nicolailund/PalletProof/src/pallet_video_recorder/config.py

from __future__ import annotations

import tomllib
from dataclasses import dataclass, field
from pathlib import Path
import re
from typing import Any


@dataclass(frozen=True)
class CameraConfig:
    backend: str = "auto"
    width: int = 1920
    height: int = 1080
    preview_width: int = 1280
    preview_height: int = 720
    fps: int = 30
    bitrate: int = 12_000_000
    opencv_device: int = 0
    opencv_fourcc: str = "MJPG"
    autofocus_mode: str = "continuous"
    autofocus_range: str = "full"
    autofocus_speed: str = "fast"


@dataclass(frozen=True)
class BarcodeConfig:
    enabled: bool = False
    scan_every_n_frames: int = 2
    min_chars: int = 4
    max_chars: int = 64
    accepted_pattern: str = r"^[A-Za-z0-9_.()$/+%-]+$"
    roi: tuple[float, float, float, float] = (0.0, 0.0, 1.0, 1.0)
    rotation_degrees: tuple[int, ...] = (
        0,
        90,
        180,
        270,
        15,
        345,
        30,
        330,
    )
    formats: tuple[str, ...] = (
        "Code128",
        "Code39",
        "Code93",
        "Codabar",
        "ITF",
        "EAN13",
        "EAN8",
        "UPCA",
        "UPCE",
        "QRCode",
        "DataMatrix",
        "PDF417",
    )
    scan_scales: tuple[float, ...] = (1.0,)
    preprocess: bool = False
    confirm_read_count: int = 2
    confirm_window_seconds: float = 1.5
    duplicate_suppress_seconds: float = 8.0
    ambient_suppress_seconds: float = 2.0
    ambient_absent_seconds: float = 2.0
    validate_gs1_ai01_check_digit: bool = True


@dataclass(frozen=True)
class HardwareScannerConfig:
    enabled: bool = True
    mode: str = "auto"
    device: str = "auto"
    baudrate: int = 115200
    reconnect_seconds: float = 5.0
    line_idle_seconds: float = 0.25
    trigger_gpio_enabled: bool = False
    trigger_gpio_pin: int = 23
    trigger_interval_seconds: float = 2.0
    trigger_pulse_seconds: float = 0.15
    trigger_active_high: bool = False
    duplicate_suppress_seconds: float = 2.0
    min_chars: int = 4
    max_chars: int = 512
    accepted_pattern: str = r"^[A-Za-z0-9_.()$/+%-]+$"
    validate_gs1_ai01_check_digit: bool = True


@dataclass(frozen=True)
class MotionConfig:
    roi: tuple[float, float, float, float] = (0.08, 0.08, 0.84, 0.84)
    threshold: float = 0.018
    still_seconds: float = 4.0
    minimum_recording_seconds: float = 30.0
    maximum_recording_seconds: float = 180.0
    require_motion_before_stop: bool = True


@dataclass(frozen=True)
class RecordingConfig:
    root_dir: Path = Path("data")
    file_extension: str = ".mp4"


@dataclass(frozen=True)
class DeviceConfig:
    provisioning_required: bool = False
    identity_file: Path = Path("device_identity.json")
    serial_number: str = "UNPROVISIONED"
    provisioning_qr_prefix: str = "PALLETPROOF"


@dataclass(frozen=True)
class CloudConfig:
    enabled: bool = False
    supabase_url: str = ""
    supabase_anon_key: str = ""
    heartbeat_interval_seconds: float = 60.0
    request_timeout_seconds: float = 10.0
    temperature_file: Path = Path("/sys/class/thermal/thermal_zone0/temp")


@dataclass(frozen=True)
class PrivacyConfig:
    enabled: bool = False
    face_blur: bool = True
    delete_source_after_processing: bool = True
    fixed_masks: tuple[tuple[float, float, float, float], ...] = ()


@dataclass(frozen=True)
class SoundConfig:
    enabled: bool = False
    gpio_pin: int = 18
    duration_seconds: float = 0.12


@dataclass(frozen=True)
class StatusLightConfig:
    enabled: bool = True
    backend: str = "gpio"
    red_gpio_pin: int = 27
    green_gpio_pin: int = 17
    yellow_gpio_pin: int | None = None
    active_high: bool = True
    scan_flash_seconds: float = 0.4
    sysfs_led_name: str = "ACT"
    restore_trigger: str = "mmc0"


@dataclass(frozen=True)
class PreviewConfig:
    enabled: bool = False
    host: str = "0.0.0.0"
    port: int = 8080
    max_fps: float = 5.0
    width: int = 960
    jpeg_quality: int = 70


@dataclass(frozen=True)
class UploadConfig:
    enabled: bool = True
    protocol: str = "sftp"
    host: str = ""
    port: int = 22
    username: str = ""
    password: str = ""
    remote_dir: str = "/"
    passive: bool = True
    timeout_seconds: int = 30
    retry_seconds: int = 20
    delete_after_upload: bool = False
    temp_suffix: str = ".part"
    supabase_bucket: str = "videos"
    supabase_prefix: str = "device-uploads"


@dataclass(frozen=True)
class SoftwareUpdateConfig:
    enabled: bool = False
    manifest_url: str = "https://raw.githubusercontent.com/nicolailund/PalletProof/main/updates/palletproof-update.json"
    repository_dir: Path = Path(".")
    state_file: Path = Path("software_update_state.json")
    install_command: str = "bash scripts/install_from_github.sh"
    check_interval_seconds: float = 300.0
    request_timeout_seconds: float = 10.0
    install_timeout_seconds: float = 600.0
    idle_grace_seconds: float = 15.0
    apply_retry_seconds: float = 300.0
    night_start_hour: int = 2
    night_end_hour: int = 4


@dataclass(frozen=True)
class Paths:
    root: Path
    in_progress: Path
    pending: Path
    uploaded: Path
    failed: Path

    @classmethod
    def from_root(cls, root: Path) -> "Paths":
        return cls(
            root=root,
            in_progress=root / "in-progress",
            pending=root / "pending",
            uploaded=root / "uploaded",
            failed=root / "failed",
        )

    def ensure(self) -> None:
        for path in (self.root, self.in_progress, self.pending, self.uploaded, self.failed):
            path.mkdir(parents=True, exist_ok=True)


@dataclass(frozen=True)
class AppConfig:
    camera: CameraConfig = field(default_factory=CameraConfig)
    barcode: BarcodeConfig = field(default_factory=BarcodeConfig)
    hardware_scanner: HardwareScannerConfig = field(default_factory=HardwareScannerConfig)
    motion: MotionConfig = field(default_factory=MotionConfig)
    recording: RecordingConfig = field(default_factory=RecordingConfig)
    device: DeviceConfig = field(default_factory=DeviceConfig)
    cloud: CloudConfig = field(default_factory=CloudConfig)
    privacy: PrivacyConfig = field(default_factory=PrivacyConfig)
    sound: SoundConfig = field(default_factory=SoundConfig)
    status_light: StatusLightConfig = field(default_factory=StatusLightConfig)
    preview: PreviewConfig = field(default_factory=PreviewConfig)
    upload: UploadConfig = field(default_factory=UploadConfig)
    software_update: SoftwareUpdateConfig = field(default_factory=SoftwareUpdateConfig)
    paths: Paths = field(default_factory=lambda: Paths.from_root(Path("data")))


def load_config(path: Path) -> AppConfig:
    with path.open("rb") as config_file:
        raw = tomllib.load(config_file)

    recording = _build_recording(raw.get("recording", {}))
    paths = Paths.from_root(recording.root_dir)

    return AppConfig(
        camera=_dataclass_from_dict(CameraConfig, raw.get("camera", {})),
        barcode=_build_barcode(raw.get("barcode", {})),
        hardware_scanner=_build_hardware_scanner(raw.get("hardware_scanner", {})),
        motion=_build_motion(raw.get("motion", {})),
        recording=recording,
        device=_build_device(raw.get("device", {})),
        cloud=_build_cloud(raw.get("cloud", {})),
        privacy=_build_privacy(raw.get("privacy", {})),
        sound=_dataclass_from_dict(SoundConfig, raw.get("sound", {})),
        status_light=_build_status_light(raw.get("status_light", {})),
        preview=_build_preview(raw.get("preview", {})),
        upload=_build_upload(raw.get("upload", {})),
        software_update=_build_software_update(raw.get("software_update", {})),
        paths=paths,
    )


def _build_recording(raw: dict[str, Any]) -> RecordingConfig:
    values = dict(raw)
    if "root_dir" in values:
        values["root_dir"] = Path(values["root_dir"])
    return _dataclass_from_dict(RecordingConfig, values)


def _build_device(raw: dict[str, Any]) -> DeviceConfig:
    values = dict(raw)
    if "identity_file" in values:
        values["identity_file"] = Path(values["identity_file"])
    config = _dataclass_from_dict(DeviceConfig, values)
    if not config.serial_number.strip():
        raise ValueError("device.serial_number cannot be empty")
    if re.fullmatch(r"[A-Za-z0-9][A-Za-z0-9_.-]{0,63}", config.serial_number.strip()) is None:
        raise ValueError("device.serial_number must be 1-64 safe characters")
    if not config.provisioning_qr_prefix:
        raise ValueError("device.provisioning_qr_prefix cannot be empty")
    if re.fullmatch(r"[A-Z0-9]+", config.provisioning_qr_prefix) is None:
        raise ValueError("device.provisioning_qr_prefix may only contain uppercase letters and numbers")
    return config


def _build_cloud(raw: dict[str, Any]) -> CloudConfig:
    values = dict(raw)
    if "temperature_file" in values:
        values["temperature_file"] = Path(values["temperature_file"])
    config = _dataclass_from_dict(CloudConfig, values)
    if config.enabled and not config.supabase_url.strip():
        raise ValueError("cloud.supabase_url cannot be empty when cloud is enabled")
    if config.enabled and not config.supabase_anon_key.strip():
        raise ValueError("cloud.supabase_anon_key cannot be empty when cloud is enabled")
    if config.heartbeat_interval_seconds <= 0:
        raise ValueError("cloud.heartbeat_interval_seconds must be positive")
    if config.request_timeout_seconds <= 0:
        raise ValueError("cloud.request_timeout_seconds must be positive")
    return config


def _build_barcode(raw: dict[str, Any]) -> BarcodeConfig:
    values = dict(raw)
    if "roi" in values:
        values["roi"] = _roi_tuple(values["roi"])
    if "rotation_degrees" in values:
        values["rotation_degrees"] = _int_tuple(values["rotation_degrees"], "rotation_degrees")
    if "formats" in values:
        values["formats"] = _str_tuple(values["formats"], "formats")
    if "scan_scales" in values:
        values["scan_scales"] = _positive_float_tuple(values["scan_scales"], "scan_scales")

    config = _dataclass_from_dict(BarcodeConfig, values)
    if config.scan_every_n_frames < 1:
        raise ValueError("barcode.scan_every_n_frames must be at least 1")
    if config.min_chars < 1 or config.max_chars < config.min_chars:
        raise ValueError("barcode min/max character limits are invalid")
    if config.confirm_read_count < 1:
        raise ValueError("barcode.confirm_read_count must be at least 1")
    if config.confirm_window_seconds <= 0:
        raise ValueError("barcode.confirm_window_seconds must be positive")
    if config.duplicate_suppress_seconds < 0:
        raise ValueError("barcode.duplicate_suppress_seconds cannot be negative")
    if config.ambient_suppress_seconds < 0:
        raise ValueError("barcode.ambient_suppress_seconds cannot be negative")
    if config.ambient_absent_seconds <= 0:
        raise ValueError("barcode.ambient_absent_seconds must be positive")
    return config


def _build_hardware_scanner(raw: dict[str, Any]) -> HardwareScannerConfig:
    config = _dataclass_from_dict(HardwareScannerConfig, dict(raw))
    if config.mode not in {"auto", "serial", "hid_keyboard"}:
        raise ValueError("hardware_scanner.mode must be 'auto', 'serial' or 'hid_keyboard'")
    if not config.device:
        raise ValueError("hardware_scanner.device cannot be empty")
    if config.baudrate <= 0:
        raise ValueError("hardware_scanner.baudrate must be positive")
    if config.reconnect_seconds <= 0:
        raise ValueError("hardware_scanner.reconnect_seconds must be positive")
    if config.line_idle_seconds < 0:
        raise ValueError("hardware_scanner.line_idle_seconds cannot be negative")
    if config.trigger_interval_seconds <= 0:
        raise ValueError("hardware_scanner.trigger_interval_seconds must be positive")
    if config.trigger_pulse_seconds < 0:
        raise ValueError("hardware_scanner.trigger_pulse_seconds cannot be negative")
    if config.duplicate_suppress_seconds < 0:
        raise ValueError("hardware_scanner.duplicate_suppress_seconds cannot be negative")
    if config.min_chars < 1 or config.max_chars < config.min_chars:
        raise ValueError("hardware_scanner min/max character limits are invalid")
    return config


def _build_motion(raw: dict[str, Any]) -> MotionConfig:
    values = dict(raw)
    if "roi" in values:
        values["roi"] = _roi_tuple(values["roi"])
    return _dataclass_from_dict(MotionConfig, values)


def _build_privacy(raw: dict[str, Any]) -> PrivacyConfig:
    values = dict(raw)
    if "fixed_masks" in values:
        values["fixed_masks"] = tuple(_roi_tuple(mask) for mask in values["fixed_masks"])
    return _dataclass_from_dict(PrivacyConfig, values)


def _build_status_light(raw: dict[str, Any]) -> StatusLightConfig:
    config = _dataclass_from_dict(StatusLightConfig, raw)
    if config.backend not in {"gpio", "act_led"}:
        raise ValueError("status_light.backend must be 'gpio' or 'act_led'")
    if config.scan_flash_seconds < 0:
        raise ValueError("status_light.scan_flash_seconds cannot be negative")
    pins = [config.red_gpio_pin, config.green_gpio_pin]
    if config.yellow_gpio_pin is not None:
        pins.append(config.yellow_gpio_pin)
    if len(set(pins)) != len(pins):
        raise ValueError("status_light GPIO pins must be different")
    _validate_sysfs_token(config.sysfs_led_name, "status_light.sysfs_led_name")
    _validate_sysfs_token(config.restore_trigger, "status_light.restore_trigger")
    return config


def _build_preview(raw: dict[str, Any]) -> PreviewConfig:
    config = _dataclass_from_dict(PreviewConfig, raw)
    if not (1 <= config.port <= 65535):
        raise ValueError("preview.port must be between 1 and 65535")
    if config.max_fps <= 0:
        raise ValueError("preview.max_fps must be positive")
    if config.width < 0:
        raise ValueError("preview.width cannot be negative")
    if not (1 <= config.jpeg_quality <= 100):
        raise ValueError("preview.jpeg_quality must be between 1 and 100")
    return config


def _build_upload(raw: dict[str, Any]) -> UploadConfig:
    config = _dataclass_from_dict(UploadConfig, raw)
    if config.protocol.lower() not in {"ftp", "ftps", "sftp", "supabase"}:
        raise ValueError("upload.protocol must be 'ftp', 'ftps', 'sftp' or 'supabase'")
    if config.timeout_seconds <= 0:
        raise ValueError("upload.timeout_seconds must be positive")
    if config.retry_seconds <= 0:
        raise ValueError("upload.retry_seconds must be positive")
    if not config.temp_suffix:
        raise ValueError("upload.temp_suffix cannot be empty")
    if config.protocol.lower() == "supabase":
        if not config.supabase_bucket.strip():
            raise ValueError("upload.supabase_bucket cannot be empty for Supabase upload")
        _validate_storage_path_part(config.supabase_bucket, "upload.supabase_bucket")
        if config.supabase_prefix.strip():
            for part in config.supabase_prefix.strip("/").split("/"):
                _validate_storage_path_part(part, "upload.supabase_prefix")
    return config


def _build_software_update(raw: dict[str, Any]) -> SoftwareUpdateConfig:
    values = dict(raw)
    if "repository_dir" in values:
        values["repository_dir"] = Path(values["repository_dir"])
    if "state_file" in values:
        values["state_file"] = Path(values["state_file"])

    config = _dataclass_from_dict(SoftwareUpdateConfig, values)
    if config.enabled and not config.manifest_url:
        raise ValueError("software_update.manifest_url cannot be empty when updates are enabled")
    if not config.install_command.strip():
        raise ValueError("software_update.install_command cannot be empty")
    if config.check_interval_seconds <= 0:
        raise ValueError("software_update.check_interval_seconds must be positive")
    if config.request_timeout_seconds <= 0:
        raise ValueError("software_update.request_timeout_seconds must be positive")
    if config.install_timeout_seconds <= 0:
        raise ValueError("software_update.install_timeout_seconds must be positive")
    if config.idle_grace_seconds < 0:
        raise ValueError("software_update.idle_grace_seconds cannot be negative")
    if config.apply_retry_seconds < 0:
        raise ValueError("software_update.apply_retry_seconds cannot be negative")
    if not (0 <= config.night_start_hour <= 23):
        raise ValueError("software_update.night_start_hour must be between 0 and 23")
    if not (0 <= config.night_end_hour <= 23):
        raise ValueError("software_update.night_end_hour must be between 0 and 23")
    if config.night_start_hour == config.night_end_hour:
        raise ValueError("software_update night window cannot be zero hours")
    return config


def _roi_tuple(value: Any) -> tuple[float, float, float, float]:
    if len(value) != 4:
        raise ValueError(f"ROI/mask must contain 4 values, got {value!r}")
    result = tuple(float(part) for part in value)
    x, y, width, height = result
    if x < 0 or y < 0 or width <= 0 or height <= 0 or x + width > 1 or y + height > 1:
        raise ValueError(f"ROI/mask must be normalized inside the image, got {value!r}")
    return result


def _int_tuple(value: Any, name: str) -> tuple[int, ...]:
    if not value:
        raise ValueError(f"{name} must contain at least one value")
    return tuple(int(part) for part in value)


def _positive_float_tuple(value: Any, name: str) -> tuple[float, ...]:
    if not value:
        raise ValueError(f"{name} must contain at least one value")
    result = tuple(float(part) for part in value)
    if any(part <= 0 for part in result):
        raise ValueError(f"{name} values must be positive")
    return result


def _str_tuple(value: Any, name: str) -> tuple[str, ...]:
    if not value:
        raise ValueError(f"{name} must contain at least one value")
    return tuple(str(part) for part in value)


def _validate_sysfs_token(value: str, name: str) -> None:
    if re.fullmatch(r"[A-Za-z0-9:_-]+", value) is None:
        raise ValueError(f"{name} may only contain letters, numbers, colon, underscore or dash")


def _validate_storage_path_part(value: str, name: str) -> None:
    if re.fullmatch(r"[A-Za-z0-9_.-]+", value) is None:
        raise ValueError(f"{name} may only contain letters, numbers, dot, underscore or dash")


def _dataclass_from_dict(cls: type[Any], values: dict[str, Any]) -> Any:
    field_names = set(cls.__dataclass_fields__)  # type: ignore[attr-defined]
    unknown = set(values) - field_names
    if unknown:
        raise ValueError(f"Unknown config keys for {cls.__name__}: {sorted(unknown)}")
    return cls(**values)
